pdaehne/DSUB19-Adapter/images/Adapter_on_Atari_ST.jpg

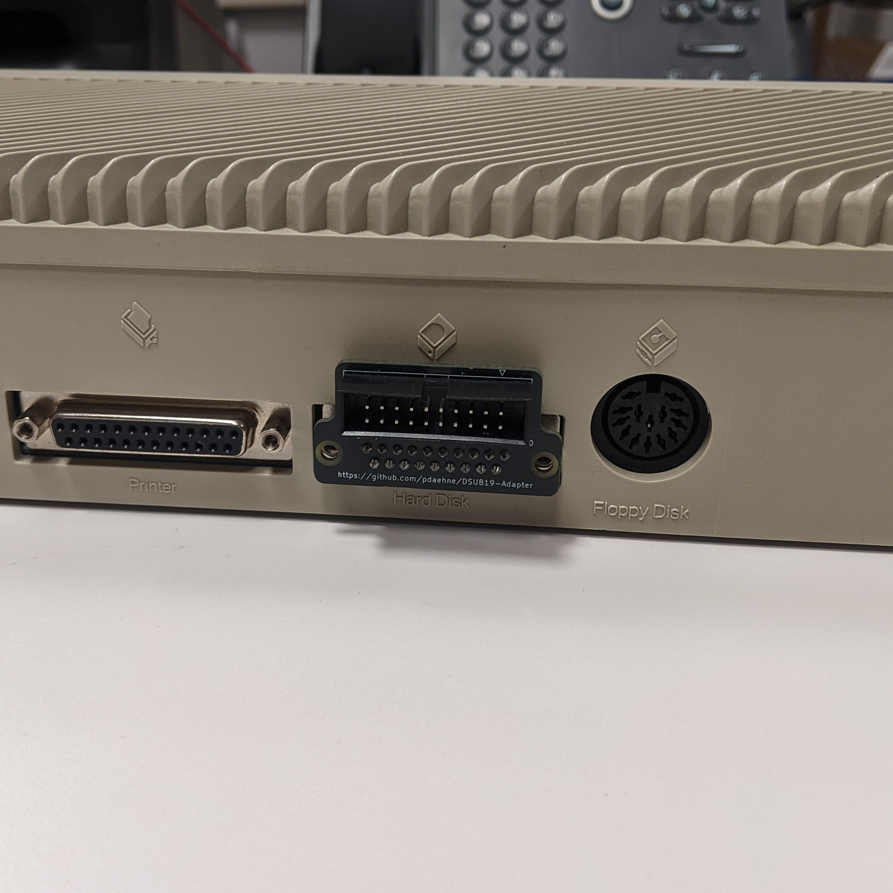
images/Adapter_on_Atari_ST.jpg
