pdaehne/DSUB19-Adapter/DSUB19-Adapter.kicad_sch

## KiCad design DSUB19-Adapter.kicad_sch (2025-01-20)

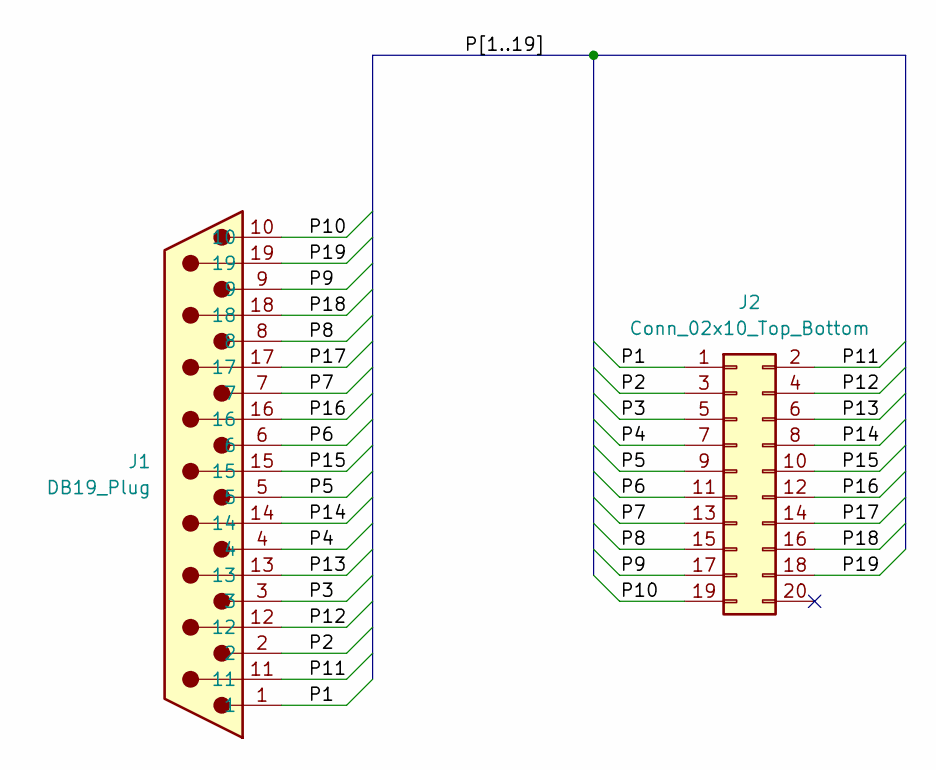
[picture p12: schematic DSUB19-Adapter.kicad_sch]

Parts:
J1: DB19_Plug; DB19
J2: Conn_02x10_Top_Bottom; IDC-Header_2x10_P2.54mm_Vertical

Connections:
P1: J1.1, J2.1
P2: J1.2, J2.3
P3: J1.3, J2.5
P4: J1.4, J2.7
P5: J1.5, J2.9
P6: J1.6, J2.11
P7: J1.7, J2.13
P8: J1.8, J2.15
P9: J1.9, J2.17
P10: J1.10, J2.19
P11: J1.11, J2.2
P12: J1.12, J2.4
P13: J1.13, J2.6
P14: J1.14, J2.8
P15: J1.15, J2.10
P16: J1.16, J2.12
P17: J1.17, J2.14
P18: J1.18, J2.16
P19: J1.19, J2.18
